Iver-Iscariot/Large-format-foam-insert/IMG_0497.jpg

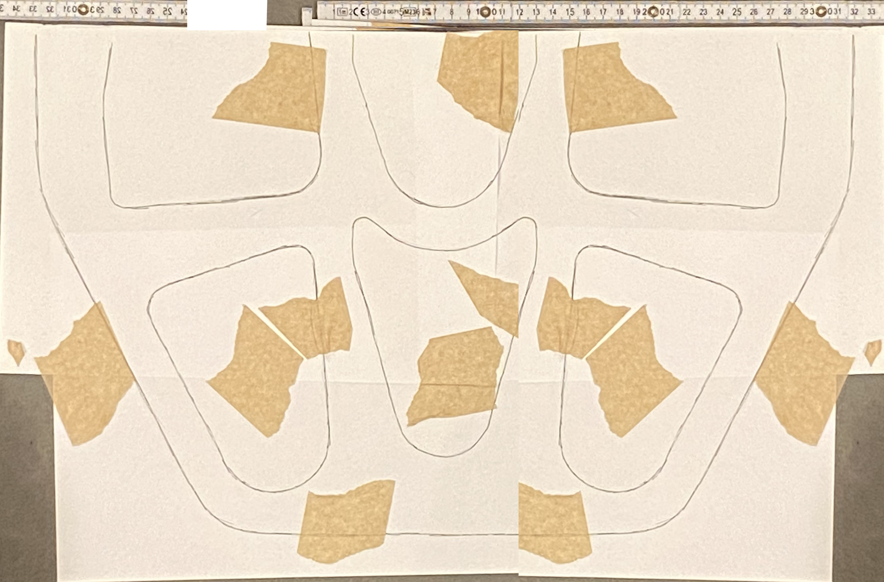
IMG_0497.jpg
